linyuxuanlin/CASTIC/3D打印模型/6659BA9AB44FA2074E64B98FD48E9A64.jpg

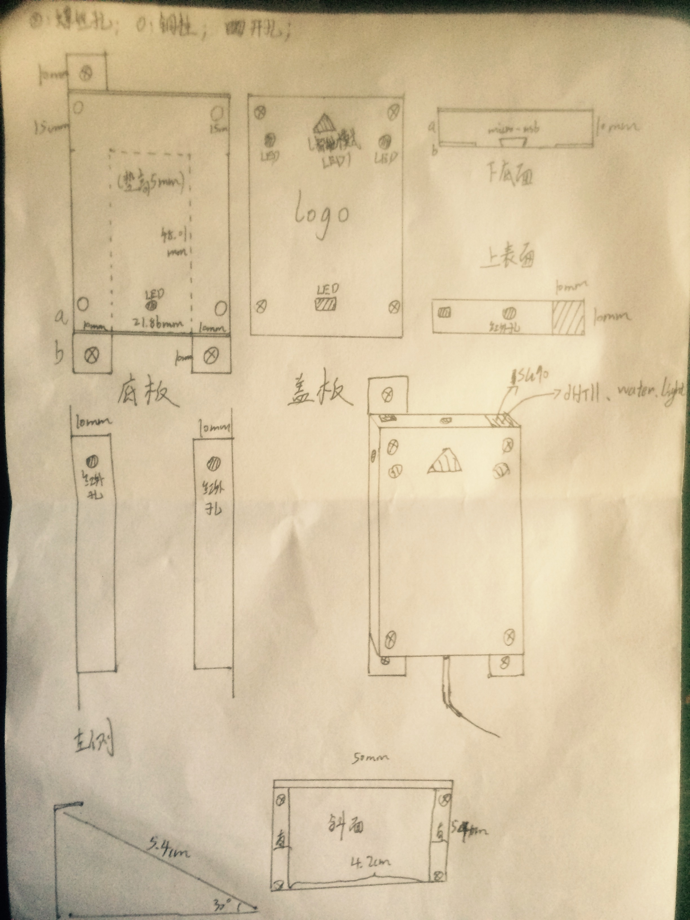
3D打印模型/6659BA9AB44FA2074E64B98FD48E9A64.jpg
