linyuxuanlin/CASTIC/专利相关/其他文件/灯座流程图.png

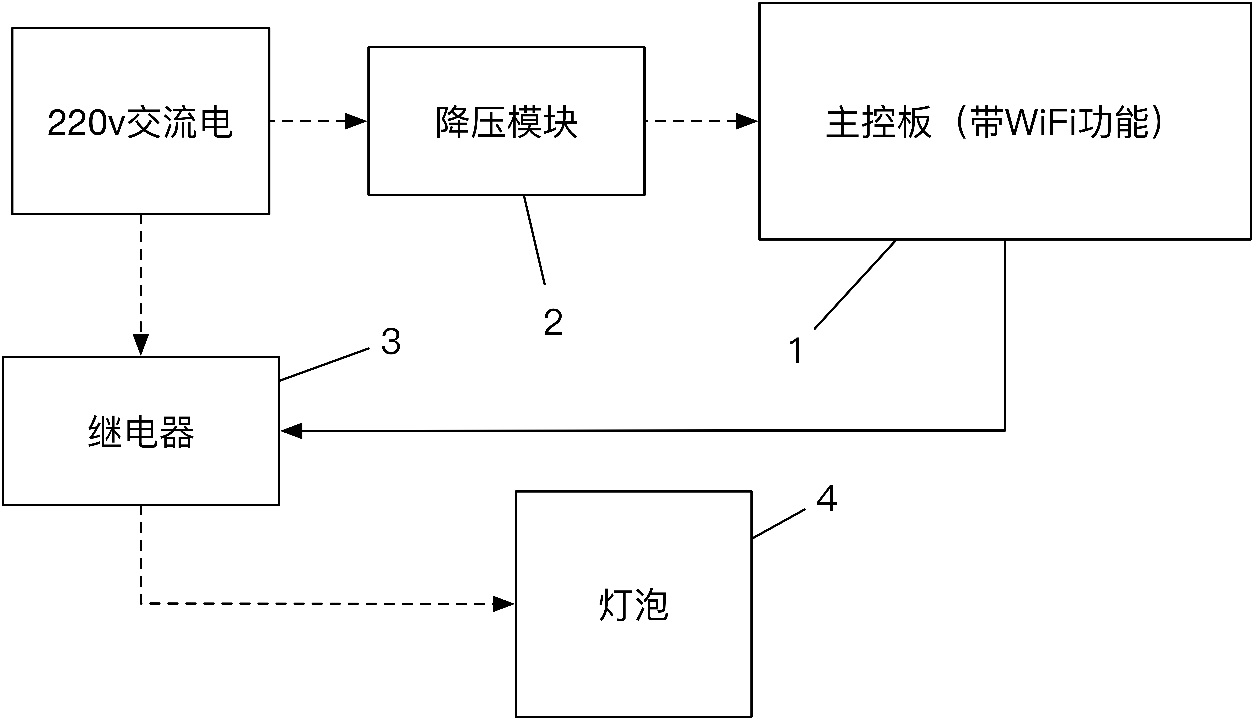
专利相关/其他文件/灯座流程图.png
