linyuxuanlin/CASTIC/展示宣传画/默认标题--设计创建于创客贴 (3).png

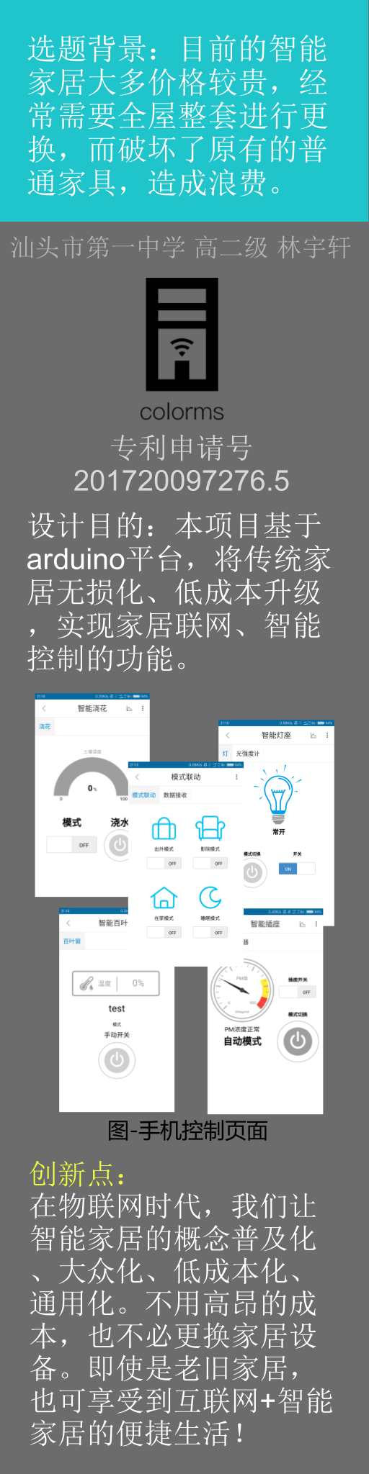
展示宣传画/默认标题--设计创建于创客贴 (3).png
